khinds10/WeatherJar/settings-shadow.py

#!/usr/bin/python
# Kevin Hinds http://www.kevinhinds.com
# License: GPL 2.0

# forecast.io API key for local weather information
weatherAPIURL = 'https://api.forecast.io/forecast/'
weatherAPIKey = 'API KEY HERE'

# temperature API to get the colors
tempColorAPI = 'http://www.mytempuratureapi.com'

# search google to get the Latitude/Longitude for your home location
latitude = 42
longitude = -71
